TIPConsulting/QTPY_ClimbingCompanion/ComputeCapsule/Capsule Render Ortho Front.png

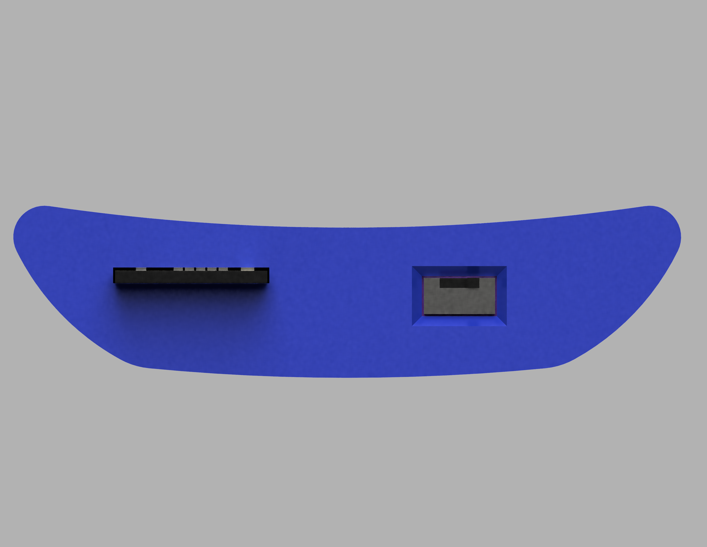
ComputeCapsule/Capsule Render Ortho Front.png
