TIPConsulting/QTPY_ClimbingCompanion/ComputeCapsule/Capsule Render Ortho Side.png

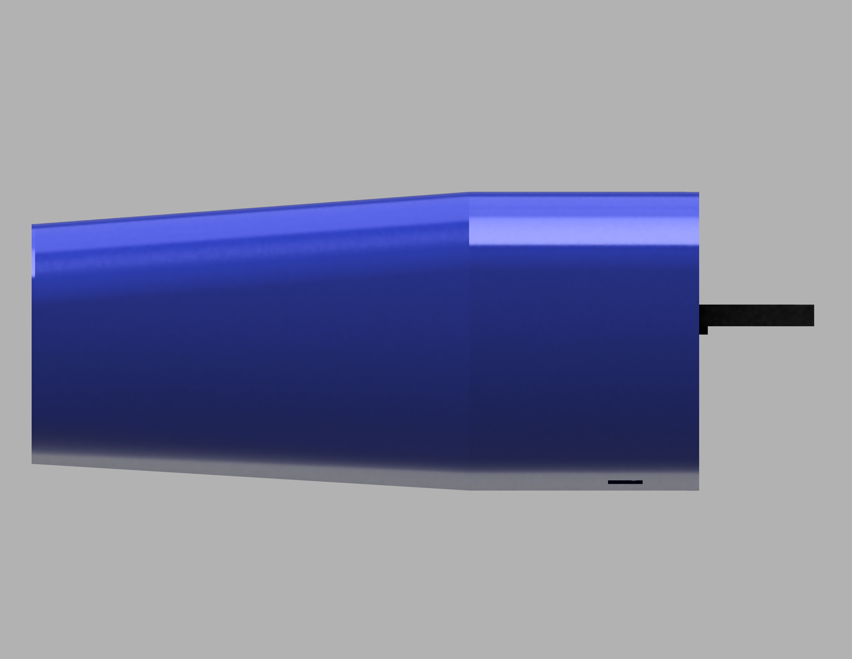
ComputeCapsule/Capsule Render Ortho Side.png
