TIPConsulting/QTPY_ClimbingCompanion/ComputeCapsule/Capsule Render Ortho Top.png

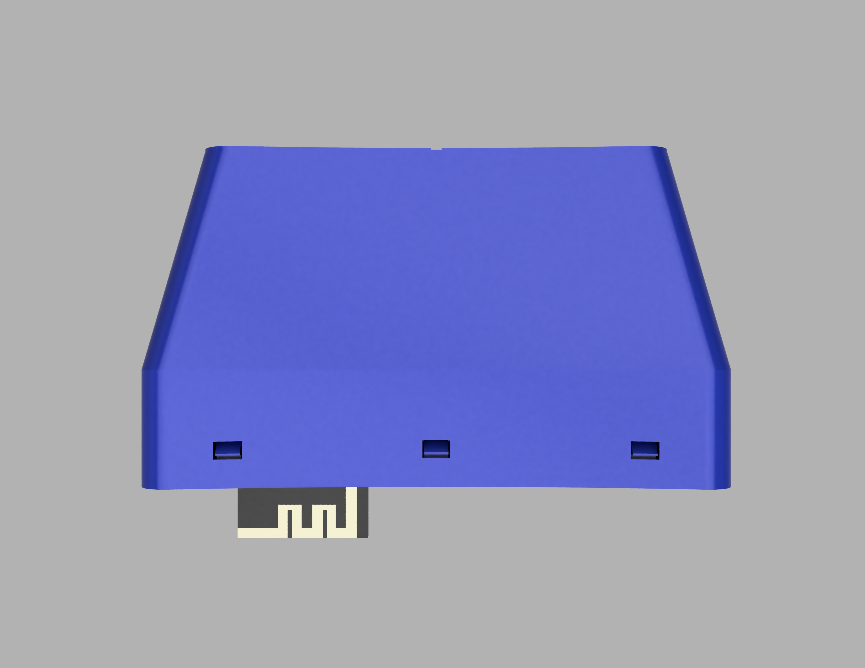
ComputeCapsule/Capsule Render Ortho Top.png
