TIPConsulting/QTPY_ClimbingCompanion/ComputeCapsule/Capsule Render.png

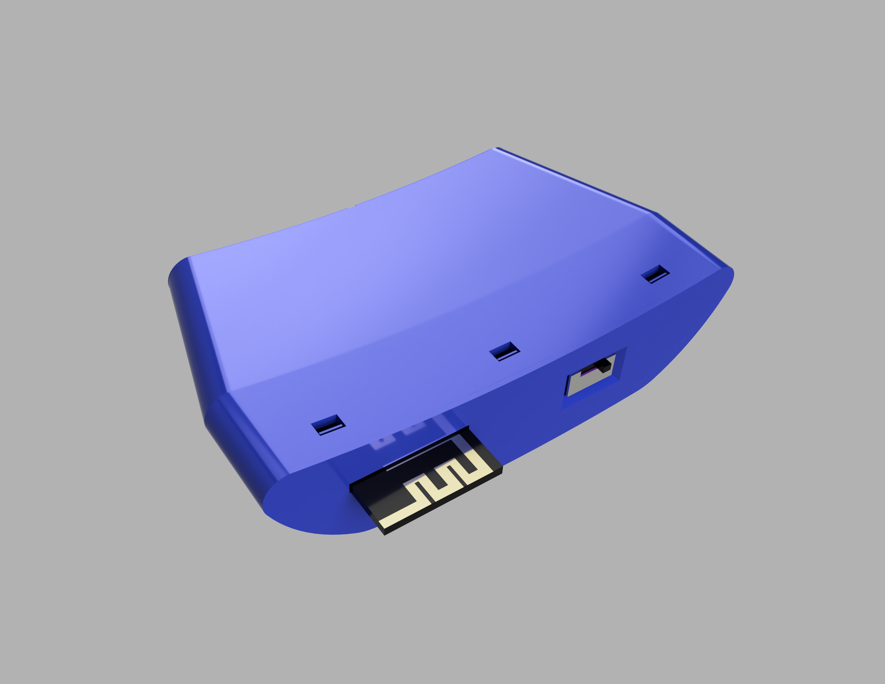
ComputeCapsule/Capsule Render.png
