TIPConsulting/QTPY_ClimbingCompanion/Documents/Helmet2_Fin (Medium).JPG

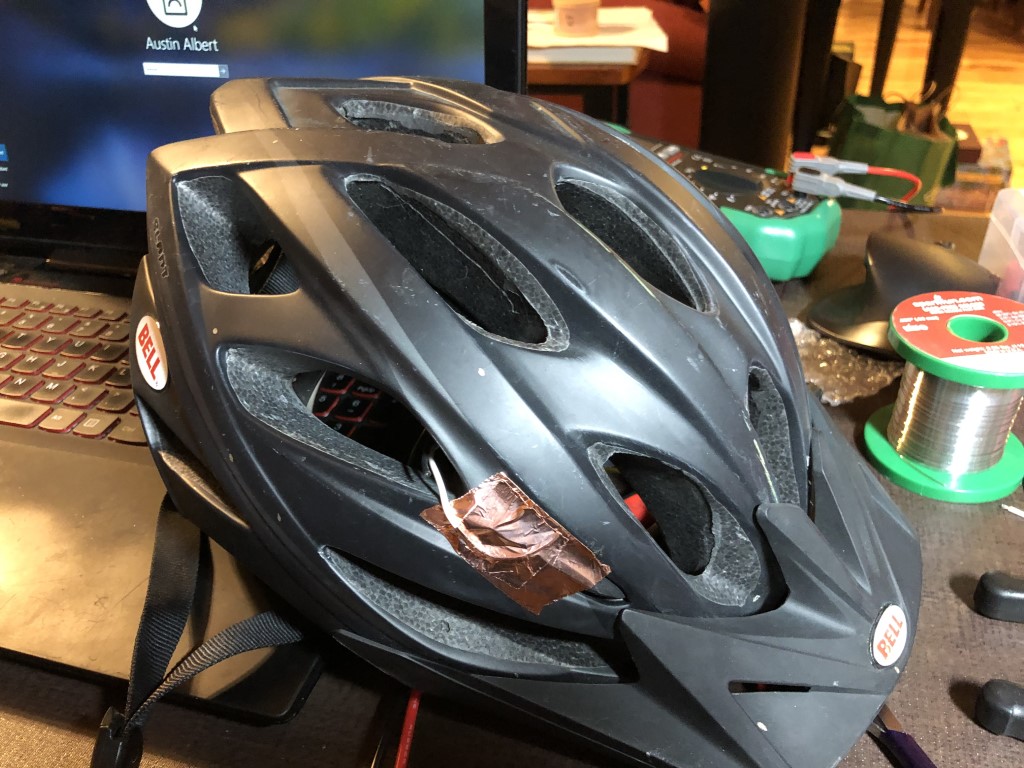
Documents/Helmet2_Fin (Medium).JPG
