TIPConsulting/QTPY_ClimbingCompanion/Documents/Helmet_FinBackOblL (Medium).JPG

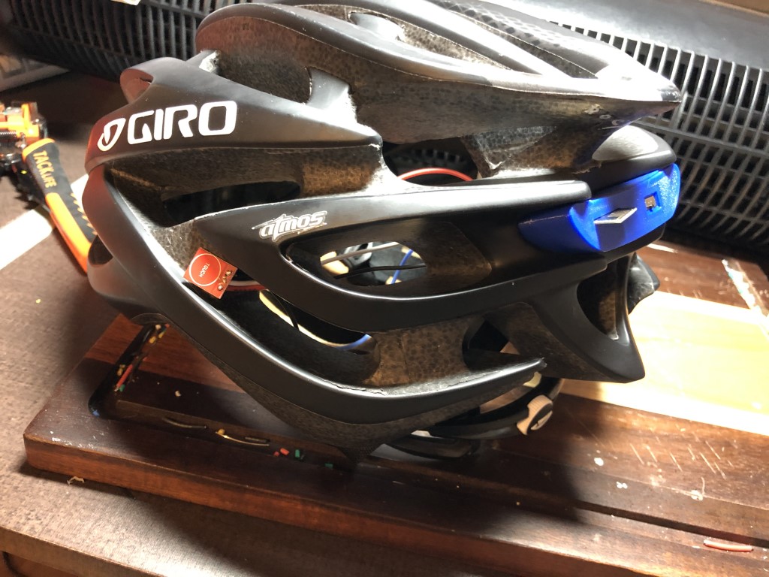
Documents/Helmet_FinBackOblL (Medium).JPG
